alexiatsikri/Ebook_reader-TSC/Images/PCB-update.png

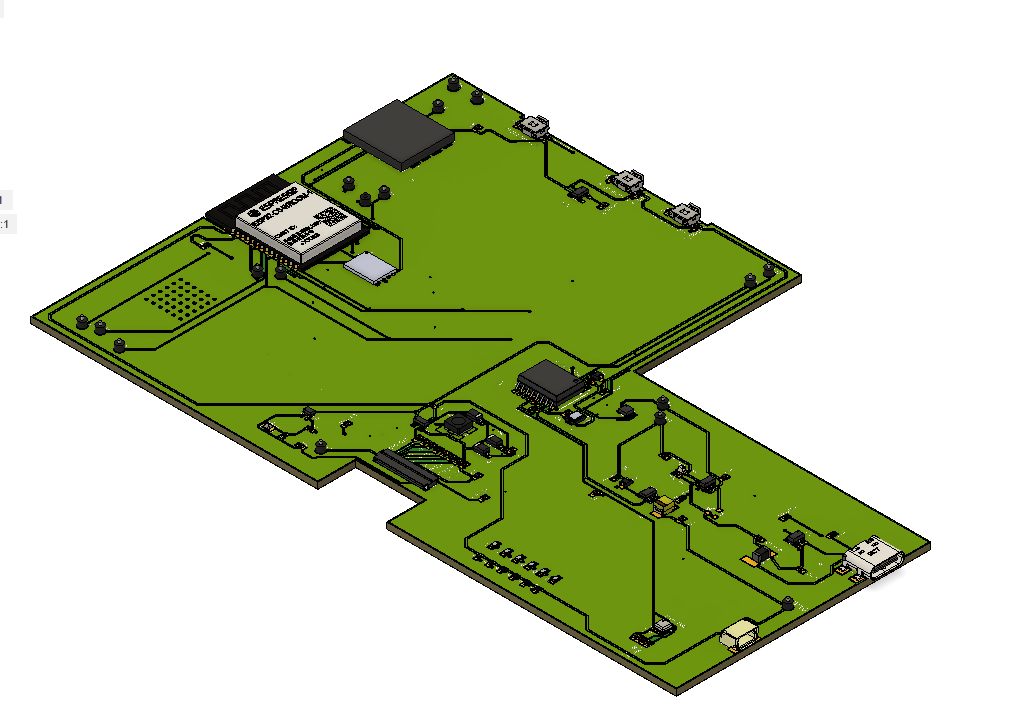
Images/PCB-update.png
